judge2005/BambuLights/src/MQTTHABroker.cpp

#include <IPAddress.h>
#include <WiFi.h>
#include <AsyncWiFiManager.h>
#include <ArduinoJson.h>
#include <ConfigItem.h>
#include <BambuLights.h>
#include <MQTTBroker.h>

#include "MQTTHABroker.h"

extern AsyncWiFiManager wifiManager;
extern const char *manifest[];
extern void setLightModeChangeCallback(std::function<void()> callback);
extern void setLightStateChangeCallback(std::function<void()> callback);
extern void broadcastUpdate(String originalKey, const BaseConfigItem& item);
extern CompositeConfigItem rootConfig;
extern MQTTBroker mqttBroker;

// disconnected, idle, printing, no_lights, error, warning
std::map<MQTTBroker::State, std::string> MQTTHABroker::PRINTER_STATES = {
    {MQTTBroker::disconnected, "disconnected"},
    {MQTTBroker::idle, "idle"},
    {MQTTBroker::printing, "printing"},
    {MQTTBroker::no_lights, "no_lights"},
    {MQTTBroker::error, "error"},
    {MQTTBroker::warning, "warning"}
};

const char *MQTTHABroker::effectNames[] = {
    "White",
    "Reactive",
    0
};

MQTTHABroker::MQTTHABroker() {
}

void MQTTHABroker::onConnect(bool sessionPresent)
{
    connected = true;
	reconnect = false;
    client.subscribe("homeassistant/status", 2);
    sendHADiscoveryMessage();
}

#ifdef ASYNC_MTTT_HA_CLIENT
void MQTTHABroker::onDisconnect(AsyncMqttClientDisconnectReason reason)
#else
void MQTTHABroker::onDisconnect(espMqttClientTypes::DisconnectReason reason)
#endif
{
	Serial.printf("Disconnected from HA: %u\n", static_cast<uint8_t>(reason));

    connected = false;
    reconnect = true;
    lastReconnect = millis();
}

#ifdef ASYNC_MTTT_HA_CLIENT
void MQTTHABroker::onMessage(char* topic, char* payload, AsyncMqttClientMessageProperties properties, size_t length, size_t index, size_t total_length)
#else
void MQTTHABroker::onMessage(const espMqttClientTypes::MessageProperties& properties, const char* topic, const uint8_t* payload, size_t length, size_t index, size_t total_length)
#endif
{
	static uint8_t mqttMessageBuffer[256];

		// payload is bigger then max: return chunked
	if (total_length >= sizeof(mqttMessageBuffer)) {
		DEBUG("MQTT_HA message too large");
		return;
	}

	// add data and dispatch when done
	memcpy(&mqttMessageBuffer[index], payload, length);
	if (index + length == total_length) {
		// message is complete here
		mqttMessageBuffer[total_length] = 0;
        onCompleteMessage(properties, topic, mqttMessageBuffer, total_length);
	}
}

#ifdef ASYNC_MTTT_HA_CLIENT
void MQTTHABroker::onCompleteMessage(char* topic, char* payload, AsyncMqttClientMessageProperties properties, size_t length)
#else
void MQTTHABroker::onCompleteMessage(const espMqttClientTypes::MessageProperties& properties, const char* topic, const uint8_t* payload, size_t length)
#endif
{
    Serial.printf("Received message %s on topic %s\n", (char*)payload, topic);

    if (strcmp(topic, "homeassistant/status") == 0) {
        if (strcmp("online", (const char*)payload)) {
            Serial.println("HA online");
            sendHADiscoveryMessage();
        }
    } else if (strcmp(topic, chamberLightCommandTopic) == 0) {
        if (strcmp((const char *)payload, "OFF") == 0) {
            mqttBroker.setChamberLight(false);
       } else if (strcmp((const char *)payload, "ON") == 0){
            mqttBroker.setChamberLight(true);
        } else {
            Serial.printf("Unknown chamber light %s\n", (const char *)payload);
        }
        broadcastUpdate(BambuLights::getLightState().name, BambuLights::getLightState());
        publishLightState();
    } else if (strcmp(topic, lightCommandTopic) == 0) {
        if (strcmp((const char *)payload, "OFF") == 0) {
            BambuLights::getLightState() = false;
       } else if (strcmp((const char *)payload, "ON") == 0){
            BambuLights::getLightState() = true;
        } else {
            Serial.printf("Unknown strip light %s\n", (const char *)payload);
        }
        broadcastUpdate(BambuLights::getLightState().name, BambuLights::getLightState());
        publishLightState();
    } else if (strcmp(topic, effectCommandTopic) == 0) {
        bool found = false;
        for (int i=0; effectNames[i] != 0; i++) {
            if (strcmp(effectNames[i], (const char *)payload) == 0) {
                BambuLights::getLightMode() = i;
                found = true;
                break;
            }
        }
        if (found) {
            broadcastUpdate(BambuLights::getLightMode().name, BambuLights::getLightMode());
        } else {
            Serial.printf("Unknown light effect %s\n", (const char*)payload);
        }
        publishEffectState();
    } else {
        Serial.print("Unknown topic: ");
        Serial.print(topic);
        Serial.print(", value: ");
        Serial.println((const char*)payload);
    }
}

void MQTTHABroker::onPrinterStateChanged(MQTTBroker* printerBroker) {
    if (client.connected()) {
        JsonDocument state;
        state["light"] = printerBroker->isLightOn() ? "ON" : "OFF";
        state["door"] = printerBroker->isDoorOpen() ? "ON" : "OFF";
        state["connection"] = printerBroker->isConnected() ? "ON" : "OFF";
        state["state"] = PRINTER_STATES[printerBroker->getState()];

        char buffer[256];
        serializeJson(state, buffer);

        uint16_t result = client.publish(printerStateTopic, 1, false, buffer);
    }
}

bool MQTTHABroker::init(const String& id) {
    this->id = id;
    mqttBroker.setStateChangedCallback([this](MQTTBroker* printerBroker) { onPrinterStateChanged(printerBroker); });

    client.disconnect();

    IPAddress ipAddress;
    if (ipAddress.fromString(getHost().value.c_str())) {
        sprintf(lightStateTopic,   "bambu_lights/%s/bambu_lights/light/state", id.c_str());
        sprintf(lightCommandTopic, "bambu_lights/%s/bambu_lights/light/set", id.c_str());
        sprintf(chamberLightCommandTopic, "bambu_lights/%s/bambu_lights/chamber_light/set", id.c_str());
        sprintf(effectStateTopic,  "bambu_lights/%s/bambu_lights/effect/state", id.c_str());
        sprintf(effectCommandTopic,"bambu_lights/%s/bambu_lights/effect/set", id.c_str());
        sprintf(printerStateTopic,"bambu_lights/%s/bambu_lights/printer/state", id.c_str());
        sprintf(availabilityTopic, "bambu_lights/%s/availability", id.c_str());
        
        client.setServer(getHost().value.c_str(), getPort());
        client.setCredentials(getUser().value.c_str(),getPassword().value.c_str());
        client.setWill(availabilityTopic, 2, true, "offline");
        client.setClientId(id.c_str());
        client.onConnect([this](bool sessionPresent) { this->onConnect(sessionPresent); });
#ifdef ASYNC_MTTT_HA_CLIENT
        client.onDisconnect([this](AsyncMqttClientDisconnectReason reason) { this->onDisconnect(reason); });
        client.onMessage([this](char* topic, char* payload, AsyncMqttClientMessageProperties properties, size_t length, size_t index, size_t total_length) {
            this->onMessage(topic, payload, properties, length, index, total_length);
        });
#else
        client.onDisconnect([this](espMqttClientTypes::DisconnectReason reason) { this->onDisconnect(reason); });
        client.onMessage([this](const espMqttClientTypes::MessageProperties& properties, const char* topic, const uint8_t* payload, size_t length, size_t index, size_t total_length) {
            this->onMessage(properties, topic, payload, length, index, total_length);
        });
#endif
        setLightModeChangeCallback([this]() { this->publishEffectState(); });
        setLightStateChangeCallback([this]() { this->publishLightState(); });
        
        reconnect = true;
    }

    return reconnect;
}

void MQTTHABroker::connect() {
    if (WiFi.isConnected() && !wifiManager.isAP()) {
        Serial.println("Connecting to MQTTHA...");
        client.connect();
    }
}

void MQTTHABroker::checkConnection() {
    if (reconnect && (millis() - lastReconnect >= 2000)) {
        lastReconnect = millis();
        connect();
    }
}

void MQTTHABroker::publishLightState() {
    if (client.connected()) {
        JsonDocument state;
        state["light"] = BambuLights::getLightState() ? "ON" : "OFF";
        char buffer[256];
        serializeJson(state, buffer);

        Serial.print(lightStateTopic);
        Serial.print(":");
        Serial.println(buffer);

        uint16_t result = client.publish(lightStateTopic, 1, false, buffer);
        Serial.printf("State send result %d\n", result);
    }
}

void MQTTHABroker::publishEffectState() {
    if (client.connected()) {
        JsonDocument state;
        state["effect"] = effectNames[BambuLights::getLightMode()];
        char buffer[256];
        serializeJson(state, buffer);

        Serial.print(effectStateTopic);
        Serial.print(":");
        Serial.println(buffer);

        uint16_t result = client.publish(effectStateTopic, 1, false, buffer);

        Serial.printf("State send result %d\n", result);
    }
}

void MQTTHABroker::sendHADiscoveryMessage() {
    client.subscribe(lightCommandTopic, 0);
    client.subscribe(effectCommandTopic, 0);
    client.subscribe(chamberLightCommandTopic, 0);

    char discoveryTopic[128];
    char buffer[1024];
    JsonDocument doc;
    size_t n;

    // This is the discovery topic for the 'light_mode' switch
    sprintf(discoveryTopic, "homeassistant/light/%s/bambu_lights/config", id.c_str());

    doc["name"] = "Bambu Lights";
    doc["icon"] = "mdi:led-strip-variant";
    doc["unique_id"] = "bambu_lights_" + id;
    doc["state_topic"] = lightStateTopic;
    doc["command_topic"] = lightCommandTopic;
    doc["avty_t"] = availabilityTopic;
    doc["state_value_template"] = "{{value_json.light}}";
    doc["effect"] = true;
    doc["effect_state_topic"] = effectStateTopic;
    doc["effect_command_topic"] = effectCommandTopic;
    doc["effect_value_template"] = "{{value_json.effect}}";
    JsonArray myArray = doc["effect_list"].to<JsonArray>();
    for (int i=0; effectNames[i] != 0; i++) {
        myArray.add(effectNames[i]);
    }
    doc["device"]["configuration_url"] = "http://" + WiFi.localIP().toString() + "/";
    doc["device"]["name"] = manifest[3];
    doc["device"]["identifiers"][0] = WiFi.macAddress();
    doc["device"]["model"] = manifest[0];
    doc["device"]["sw_version"] = manifest[1];

    n = serializeJson(doc, buffer);

    client.publish(discoveryTopic, 2, false, buffer);

    sprintf(discoveryTopic, "homeassistant/light/%s/chamber_light/config", id.c_str());

    doc.clear();

    doc["name"] = "Chamber Light";
    doc["icon"] = "mdi:light-flood-down";
    doc["unique_id"] = "chamber_light_" + id;
    doc["state_topic"] = printerStateTopic;
    doc["command_topic"] = chamberLightCommandTopic;
    doc["avty_t"] = availabilityTopic;
    doc["state_value_template"] = "{{value_json.light}}";
    doc["device"]["configuration_url"] = "http://" + WiFi.localIP().toString() + "/";
    doc["device"]["name"] = manifest[3];
    doc["device"]["identifiers"][0] = WiFi.macAddress();
    doc["device"]["model"] = manifest[0];
    doc["device"]["sw_version"] = manifest[1];

    n = serializeJson(doc, buffer);

    client.publish(discoveryTopic, 2, false, buffer);

    sprintf(discoveryTopic, "homeassistant/sensor/%s/printer_state/config", id.c_str());

    doc.clear();

    doc["name"] = "Printer State";
    doc["icon"] = "mdi:cloud-print";
    doc["unique_id"] = "printer_state" + id;
    doc["state_topic"] = printerStateTopic;
    doc["device_class"] = "enum";
    JsonArray optArray = doc["options"].to<JsonArray>();
    for (const auto& pair : MQTTHABroker::PRINTER_STATES) {
        optArray.add(pair.second.c_str());
    }
    doc["avty_t"] = availabilityTopic;
    doc["value_template"] = "{{value_json.state}}";
    doc["device"]["configuration_url"] = "http://" + WiFi.localIP().toString() + "/";
    doc["device"]["name"] = manifest[3];
    doc["device"]["identifiers"][0] = WiFi.macAddress();
    doc["device"]["model"] = manifest[0];
    doc["device"]["sw_version"] = manifest[1];

    n = serializeJson(doc, buffer);

    client.publish(discoveryTopic, 2, false, buffer);

    client.publish(availabilityTopic, 2, true, "online");

    sprintf(discoveryTopic, "homeassistant/binary_sensor/%s/door/config", id.c_str());

    doc.clear();

    doc["name"] = "Door";
    doc["unique_id"] = "door" + id;
    doc["state_topic"] = printerStateTopic;
    doc["device_class"] = "door";
    doc["avty_t"] = availabilityTopic;
    doc["value_template"] = "{{value_json.door}}";
    doc["device"]["configuration_url"] = "http://" + WiFi.localIP().toString() + "/";
    doc["device"]["name"] = manifest[3];
    doc["device"]["identifiers"][0] = WiFi.macAddress();
    doc["device"]["model"] = manifest[0];
    doc["device"]["sw_version"] = manifest[1];

    n = serializeJson(doc, buffer);

    client.publish(discoveryTopic, 2, false, buffer);

    sprintf(discoveryTopic, "homeassistant/binary_sensor/%s/connection/config", id.c_str());

    doc.clear();

    doc["name"] = "Connection";
    doc["unique_id"] = "connection" + id;
    doc["state_topic"] = printerStateTopic;
    doc["device_class"] = "connectivity";
    doc["avty_t"] = availabilityTopic;
    doc["value_template"] = "{{value_json.connection}}";
    doc["device"]["configuration_url"] = "http://" + WiFi.localIP().toString() + "/";
    doc["device"]["name"] = manifest[3];
    doc["device"]["identifiers"][0] = WiFi.macAddress();
    doc["device"]["model"] = manifest[0];
    doc["device"]["sw_version"] = manifest[1];

    n = serializeJson(doc, buffer);

    client.publish(discoveryTopic, 2, false, buffer);

    client.publish(availabilityTopic, 2, true, "online");

    publishLightState();
    publishEffectState();
    onPrinterStateChanged(&mqttBroker);
}
