judge2005/BambuLights/src/WSInfoHandler.cpp

#include <WSInfoHandler.h>
// #include <Uptime.h>
#include <ArduinoJson.h>
#include <AsyncWebSocket.h>
#include <WiFi.h>
extern "C" {
#include "esp_ota_ops.h"
#include "esp_image_format.h"
#include "esp_heap_caps.h"
}

static uint32_t sketchSize(sketchSize_t response) {
    esp_image_metadata_t data;
    const esp_partition_t *running = esp_ota_get_running_partition();
    if (!running) return 0;
    const esp_partition_pos_t running_pos  = {
        .offset = running->address,
        .size = running->size,
    };
    data.start_addr = running_pos.offset;
    esp_image_verify(ESP_IMAGE_VERIFY, &running_pos, &data);
    if (response) {
        return running_pos.size - data.image_len;
    } else {
        return data.image_len;
    }
}
    
void WSInfoHandler::handle(AsyncWebSocketClient *client, char *data) {
	cbFunc();

	// static Uptime uptime;
	JsonDocument doc;
	JsonObject root = doc.to<JsonObject>();

	root["type"] = "sv.init.info";

	JsonVariant value = root.createNestedObject("value");
	value["esp_free_iram_heap"] = heap_caps_get_free_size(MALLOC_CAP_IRAM_8BIT | MALLOC_CAP_32BIT);
	value["esp_free_heap"] = ESP.getFreeHeap();
	value["esp_free_heap_min"] = ESP.getMinFreeHeap();
	value["esp_max_alloc_heap"] = heap_caps_get_largest_free_block(MALLOC_CAP_INTERNAL);
	value["esp_sketch_size"] = sketchSize(SKETCH_SIZE_TOTAL);
	value["esp_sketch_space"] = sketchSize(SKETCH_SIZE_FREE);

	value["esp_chip_id"] = String(ESP.getChipRevision(), HEX);

	value["wifi_ip_address"] = WiFi.localIP().toString();
	value["wifi_mac_address"] = WiFi.macAddress();
	value["wifi_ssid"] = WiFi.SSID();
	value["wifi_ap_ssid"] = ssid;
	value["hostname"] = hostname;
	value["software_revision"] = revision;

    value["fs_size"] = fsSize;
    value["fs_free"] = fsFree;
	value["brightness"] = brightness;
	value["triggered"] = triggered;
	value["clock_on"] = clockOn;

	// value["up_time"] = uptime.uptime();
	value["sync_time"] = lastUpdateTime;
	value["sync_failed_msg"] = lastFailedMessage;
	value["sync_failed_cnt"] = failedCount;

	// if (pBlankingMonitor) {
	// 	value["on_time"] = pBlankingMonitor->onTime();
	// 	value["off_time"] = pBlankingMonitor->offTime();
	// }

	String serializedJSON;
	serializeJson(root, serializedJSON);
	client->text(serializedJSON);
}
